pershin/sound-20d01/software/sound-20d01-codec/encoder.h

/*
 * File:   encoder.h
 * Author: Sergey
 *
 * Created on October 29, 2023, 11:36 PM
 */

#ifndef ENCODER_H
#define ENCODER_H

int encoder_encode(int16_t *, size_t, uint8_t, FILE *);

#endif /* ENCODER_H */
