pershin/sound-20d01/software/sound-20d01-codec/plac.h

/*
 * File:   plac.h
 * Author: Sergey
 *
 * Created on October 30, 2023, 10:04 PM
 */

#ifndef PLAC_H
#define PLAC_H

#include <stdint.h>

#define PLAC_ID 0x43414c50 /* "PLAC" */

/* MISC */
#define PLAC_BUFSIZ 256
#define PLAC_NUM_CHANNELS 2
#define PLAC_BYTES_PER_SAMPLE sizeof(int16_t)
#define PLAC_BITS_PER_SAMPLE 16
#define PLAC_SAMPLE_RATE 48000

#pragma pack(push, 1)

typedef struct {
    uint32_t FormatID; /* "PLAC" */
    uint8_t Version;   /* 1 */
} PLAC_header;

typedef struct {
    uint8_t Bits;
    int16_t Min;
} PLAC_channel;

typedef struct {
    uint16_t Size;
    uint16_t NumSamples;
    uint8_t Mixres;
    PLAC_channel Left;
    PLAC_channel Right;
} PLAC_chunk;

#pragma pack(pop)

int plac_header_write(FILE *stream);
PLAC_header *plac_header_read(FILE *stream);

#endif /* PLAC_H */
