pershin/sound-20d01/software/sound-20d01-codec/utils.h

/*
 * File:   utils.h
 * Author: Sergey
 *
 * Created on November 4, 2023, 12:00 PM
 */

#ifndef UTILS_H
#define UTILS_H

long int filesize(FILE *);
uint8_t bits_needed_signed(int16_t, int16_t);

#endif /* UTILS_H */
